gerryvel/SR-Aktor/src/helper.h

#ifndef _HELPER_H_
#define _HELPER_H_

/**
 * @file helper.h
 * @author Gerry Sebb
 * @brief Hilfsfunktionen
 * @version 1.1
 * @date 2025-01-06
 * 
 * @copyright Copyright (c) 2025
 * 
 */


#include <stdio.h>
#include <time.h>
#include <Arduino.h>
#include <LITTLEFS.h>
#include <FS.h>
#include <Wire.h>
#include <WiFi.h>
#include "configuration.h"
#include <ArduinoJson.h>
#include <Preferences.h>

inline void ShowTime(){
	time_t now = time(NULL);
	struct tm tm_now;
	localtime_r(&now, &tm_now);
	char buff[100];
	strftime(buff, sizeof(buff), "%d-%m-%Y %H:%M:%S", &tm_now);
	printf("Zeit: %s\n", buff);
}

/** Freie Speichergroesse aller 5s lesen */

inline void freeHeapSpace(){
	static unsigned long last = millis();
	if (millis() - last > 5000) {
		last = millis();
    sHeapspace = ESP.getFreeHeap();
		Serial.printf("\n[MAIN] Free heap: %d bytes\n", ESP.getFreeHeap());
	}
}

/** Ausgabe WIFI Parameter und Netzwerk scannen */

inline void WiFiDiag(void) {
  Serial.println("\nWifi-Diag:");
  AP_IP = WiFi.softAPIP();
  CL_IP = WiFi.localIP();
  Serial.print("AP IP address: ");
  Serial.println(AP_IP.toString());
  Serial.print("Client IP address: ");
  Serial.println(CL_IP.toString());
  WiFi.printDiag(Serial);
  Serial.print("\nScan AP's "); 
  {
    // WiFi.scanNetworks will return the number of networks found
    int n = WiFi.scanNetworks();
    Serial.println("scan done");
    if (n == 0) {
        Serial.println("no networks found");
    } else {
        Serial.print(n);
        Serial.println(" networks found");
        for (int i = 0; i < n; ++i) 
        {
          // Print SSID and RSSI for each network found
          Serial.print(i + 1);
          Serial.print(": ");
          Serial.print(WiFi.SSID(i));
          Serial.print(" (");
          Serial.print(WiFi.RSSI(i));
          Serial.print(")");
          Serial.println((WiFi.encryptionType(i) == WIFI_AUTH_OPEN)?" ":"*");
          delay(10);
        }
    }
  }
}

/***************************** Filesystem **************************/

/**
 * @brief LittleFS, Dateien auflisten
 * 
 * @param fs 
 * @param dirname 
 * @param levels 
 */

inline void listDir(fs::FS &fs, const char * dirname, uint8_t levels){
    Serial.printf("Listing directory: %s\r\n", dirname);

    File root = fs.open(dirname);
    if(!root){
        Serial.println("- failed to open directory");
        return;
    }
    if(!root.isDirectory()){
        Serial.println(" - not a directory");
        return;
    }

    File file = root.openNextFile();
    while(file){
        if(file.isDirectory()){
            Serial.print("  DIR : ");
            Serial.println(file.name());
            if(levels){
                listDir(fs, file.path(), levels -1);
            }
        } else {
            Serial.print("  FILE: ");
            Serial.print(file.name());
            Serial.print("\tSIZE: ");
            Serial.println(file.size());
        }
        file = root.openNextFile();
    }
}

/**
 * @brief Konfiguration aus Json-Datei lesen
 * 
 * @param filename 
 */

inline void readConfig(String filename) {
	JsonDocument testDocument;
	File configFile = LittleFS.open(filename);
	if (configFile)
	{
		Serial.println("opened config file");
		DeserializationError error = deserializeJson(testDocument, configFile);

		// Test if parsing succeeds.
		if (error)
		{
			Serial.print(F("deserializeJson() failed: "));
			Serial.println(error.f_str());
			return;
		}

		Serial.println("deserializeJson ok");
		{
			Serial.println("Read Data from Config - file");
			strcpy(tAP_Config.wAP_SSID, testDocument["wAP_SSID"] | "BinarySwitch");
			strcpy(tAP_Config.wAP_IP, testDocument["wAP_IP"] | "192.168.15.25");
			strcpy(tAP_Config.wAP_Password, testDocument["wAP_Password"] | "12345678");
			strcpy(tAP_Config.wRelay1Name, testDocument["wRelay1Name"] | "Relais 1");
      strcpy(tAP_Config.wRelay2Name, testDocument["wRelay2Name"] | "Relais 2");
      strcpy(tAP_Config.wRelay3Name, testDocument["wRelay3Name"] | "Relais 3");
      // Optional NMEA2000 debug flag (use .is/.as to avoid deprecated containsKey)
      if (testDocument["n2kDebug"].is<bool>()) {
        N2kDebug = testDocument["n2kDebug"].as<bool>();
        Serial.printf("N2kDebug set to: %s\n", N2kDebug?"true":"false");
      } else if (testDocument["n2kDebug"].is<int>()) {
        N2kDebug = (testDocument["n2kDebug"].as<int>() != 0);
        Serial.printf("N2kDebug set to: %s\n", N2kDebug?"true":"false");
      }
      // Optional acceptBroadcastCommands flag
      if (testDocument["acceptBroadcastCommands"].is<bool>()) {
        AcceptBroadcastCommands = testDocument["acceptBroadcastCommands"].as<bool>();
        Serial.printf("AcceptBroadcastCommands set to: %s\n", AcceptBroadcastCommands?"true":"false");
      } else if (testDocument["acceptBroadcastCommands"].is<int>()) {
        AcceptBroadcastCommands = (testDocument["acceptBroadcastCommands"].as<int>() != 0);
        Serial.printf("AcceptBroadcastCommands set to: %s\n", AcceptBroadcastCommands?"true":"false");
      }
		}
		configFile.close();
		Serial.println("Config > file closed");
	}

	else
	{
		Serial.println("failed to load json config");
	}
}

/**
 * @brief Webseiten Eingabe in Json-Datei schreiben
 * 
 * @param json 
 * @return true 
 * @return false 
 */

inline bool writeConfig(String json)
{
    Serial.println(json);
    Serial.println("neue Konfiguration speichern");

    // Datei zum Schreiben öffnen (überschreibt alte Datei)
    File configFile = LittleFS.open("/config.json", "w");
    if (!configFile) {
        Serial.println("Config - Datei konnte nicht geöffnet werden!");
        return false;
    }

    // JSON-Dokument parsen
    JsonDocument testDocument;
    DeserializationError error = deserializeJson(testDocument, json);
    if (error) {
        Serial.print(F("deserializeJson() failed: "));
        Serial.println(error.f_str());
        configFile.close();
        return false;
    }

    // JSON in Datei schreiben
    serializeJson(testDocument, configFile);
    Serial.println("Konfiguration geschrieben...");

    // Kontrolle
    Serial.println("Konfiguration geschrieben...");
    serializeJsonPretty(testDocument, Serial);

    configFile.close();
    Serial.println("Config - Datei geschlossen");
    return true;
}

/**
 * @brief Webseiten Eingabe in Json-Datei schreiben
 * 
 * @param name 
 * @param value 
 * @return true 
 * @return false 
 */

inline bool writeWebconfig(const String& name, const String& value)
{
    Serial.println("Config > safe config data");

    File configFile = LittleFS.open("/config.json", FILE_WRITE);
    if (configFile)
    {
        Serial.println("Config > open file");
        JsonDocument testDocument;
        DeserializationError error = deserializeJson(testDocument, configFile);
        if (error)
        {
            Serial.print(F("deserializeJson() failed: "));
            Serial.println(error.f_str());
            return false;
        }

        // Update the configuration with the new value
        testDocument[name] = value;

        // Write the updated configuration back to the file
        configFile.close();
        configFile = LittleFS.open("/config.json", FILE_WRITE);
        if (!configFile)
        {
            Serial.println("failed to open config file for writing");
            return false;
        }

        serializeJson(testDocument, configFile);
        Serial.println("Config > write data...");

        // neue Config in Serial ausgeben zur Kontrolle
        serializeJsonPretty(testDocument, Serial);

        Serial.println("Config > closed file");
        configFile.close();
    }
    else
    {
        Serial.println("failed to open config file");
        return false;
    }
    return true;
}

/***************************** I2C Bus **************************/
/** I2C Bus auslesen, alle Geräte mit Adresse ausgegeben */

inline void I2C_scan(void){
  byte error, address;
  int nDevices;
  Serial.println("Scanning...");
  nDevices = 0;
  for(address = 1; address < 127; address++ ) 
  {
    Wire.beginTransmission(address);
    error = Wire.endTransmission();
    if (error == 0) 
    {
      Serial.print("I2C device found at address 0x");
      if (address<16) 
      {
        Serial.print("0");
      }
      Serial.println(address,HEX);
      nDevices++;
    }
    else if (error==4) 
    {
      Serial.print("Unknow error at address 0x");
      if (address<16) 
      {
        Serial.print("0");
      }
      Serial.println(address,HEX);
      nDevices++;
    }
    else if (error==4) {
      Serial.print("Unknow error at address 0x");
      if (address<16) {
        Serial.print("0");
      }
      Serial.println(address,HEX);
    }    
  }
  if (nDevices == 0) {
    Serial.println("No I2C devices found\n");
  }
  else {
    Serial.println("done\n");
  }
}

/**
 * @brief WIFI Status lesen
 * 
 * @param Status 
 * @return String 
 */

inline String sWifiStatus(int Status)
{
  switch(Status){
    case WL_IDLE_STATUS:return "Warten";
    case WL_NO_SSID_AVAIL:return "Keine SSID vorhanden";
    case WL_SCAN_COMPLETED:return "Scan komlett";
    case WL_CONNECTED:return "Verbunden";
    case WL_CONNECT_FAILED:return "Verbindung fehlerhaft";
    case WL_CONNECTION_LOST:return "Verbindung verloren";
    case WL_DISCONNECTED:return "Nicht verbunden";
    default:return "unbekannt";
  }
}

/**
 * @brief Convert string to char
 * 
 * @param command 
 * @return char* 
 */

inline char* toChar(String command){
    if(command.length()!=0){
        char *p = const_cast<char*>(command.c_str());
        return p;
    }
    else{
      return 0;
    }
}

#endif
