gerryvel/SR-Aktor/src/LED.h

/**
 * @file LED.h
 * @author Gerry Sebb
 * @brief LED Ansteuerung
 * @version 2.1
 * @date 2025-01-06
 * 
 * @copyright Copyright (c) 2025
 * 
 */

#include <arduino.h>
#include "task.h"

//Configuration LED
//const int LEDBoard = 2;  //DevModule
//const int LEDBoard = 13;   //Adafruit Huzzah32

enum LED {
  Red = 19, 
  Green = 21, 
  Blue = 18,
  LEDBoard = 13 //Adafruit Huzzah32
};

void LEDblink(int PIN = LEDBoard) {
  taskBegin();
  while (1) {  // blockiert dank der TaskPause nicht 
    digitalWrite(PIN, HIGH);  // LED ein
    taskPause(250);   // gibt Rechenzeit ab         
    digitalWrite(PIN, LOW);   // LED aus
    taskPause(1000);   // gibt Rechenzeit ab         
  }
  taskEnd();   
}

void LEDflash(int PIN = LEDBoard) {
  taskBegin();
  while (1) {  // blockiert dank der TaskPause nicht 
    digitalWrite(PIN, HIGH);  // LED ein
    delay(5);
    //taskPause(2);   // gibt Rechenzeit ab    
    digitalWrite(PIN, LOW);   // LED aus
    taskPause(3000);   // gibt Rechenzeit ab    
  }
  taskEnd();   
}

void flashLED(int PIN = LEDBoard) {
  if (millis() % 1000 > 500) {
    digitalWrite(PIN, HIGH);
  } else {
    digitalWrite(PIN, LOW);
  }
}

/**
 * @brief Start Initialisierung
 * LEDtest
 */
void LEDInit() {                        
  pinMode(LED::Red, OUTPUT);
  pinMode(LED::Blue, OUTPUT);
  pinMode(LED::Green, OUTPUT);
  digitalWrite(LED::Red, HIGH);
  delay(250);
  digitalWrite(LED::Red, LOW);
  digitalWrite(LED::Blue, HIGH);
  delay(250);
  digitalWrite(LED::Blue, LOW);
  digitalWrite(LED::Green, HIGH);
  delay(250);
  digitalWrite(LED::Green, LOW);
}

void LEDon(int PIN = LEDBoard) {
  digitalWrite(PIN, HIGH);    
}

void LEDoff(int PIN = LEDBoard) {
  digitalWrite(PIN, LOW);
}

void LEDoff_RGB() {
  digitalWrite(LED::Blue, LOW);
  digitalWrite(LED::Green, LOW);
  digitalWrite(LED::Red, LOW);
}
